Squantor/embedded_ui/software/embedded_ui_mini/src/strings.cpp

/*
SPDX-License-Identifier: MIT

Copyright (c) 2022 Bart Bilos
For conditions of distribution and use, see LICENSE file
*/
/*
Common used strings
*/

#include <strings.hpp>

const char strHello[] = "Embedded user interface demo\r\n";
const char strCrLf[] = "\r\n";
